nmittow/iot-rgb-7-seg-clock/Code/esp32/ESP32AlarmClockController/APA1027SEG_digitMasks.h

CRGB digitMasks[11][21] =
{
  /* 0 */
  {
    (CRGB::Black, CRGB::Black, CRGB::Black), (CRGB::Black, CRGB::Black, CRGB::Black), (CRGB::Black, CRGB::Black, CRGB::Black),
    (CRGB::Black, CRGB::Black, CRGB::Black), (CRGB::Black, CRGB::Black, CRGB::Black), (CRGB::Black, CRGB::Black, CRGB::Black),
    (CRGB::Black, CRGB::Black, CRGB::Black), (CRGB::Black, CRGB::Black, CRGB::Black), (CRGB::Black, CRGB::Black, CRGB::Black),
    (CRGB::Black, CRGB::Black, CRGB::Black), (CRGB::Black, CRGB::Black, CRGB::Black), (CRGB::Black, CRGB::Black, CRGB::Black),
    (CRGB::Black, CRGB::Black, CRGB::Black), (CRGB::Black, CRGB::Black, CRGB::Black), (CRGB::Black, CRGB::Black, CRGB::Black),
    (CRGB::Black, CRGB::Black, CRGB::Black), (CRGB::Black, CRGB::Black, CRGB::Black), (CRGB::Black, CRGB::Black, CRGB::Black),
    (CRGB::White, CRGB::White, CRGB::White), (CRGB::White, CRGB::White, CRGB::White), (CRGB::White, CRGB::White, CRGB::White)
  },
  /* 1 */
  {
    (CRGB::White, CRGB::White, CRGB::White), (CRGB::White, CRGB::White, CRGB::White), (CRGB::White, CRGB::White, CRGB::White),
    (CRGB::Black, CRGB::Black, CRGB::Black), (CRGB::Black, CRGB::Black, CRGB::Black), (CRGB::Black, CRGB::Black, CRGB::Black),
    (CRGB::Black, CRGB::Black, CRGB::Black), (CRGB::Black, CRGB::Black, CRGB::Black), (CRGB::Black, CRGB::Black, CRGB::Black),
    (CRGB::White, CRGB::White, CRGB::White), (CRGB::White, CRGB::White, CRGB::White), (CRGB::White, CRGB::White, CRGB::White),
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
    (CRGB::White, CRGB::White, CRGB::White), (CRGB::White, CRGB::White, CRGB::White), (CRGB::White, CRGB::White, CRGB::White),
    (CRGB::White, CRGB::White, CRGB::White), (CRGB::White, CRGB::White, CRGB::White), (CRGB::White, CRGB::White, CRGB::White)
  }
};
